Swap-File/portal-gun-4/internet/http/portalguns/assets/1.png

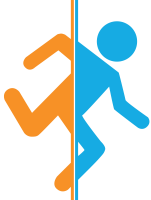
internet/http/portalguns/assets/1.png
