Swap-File/portal-gun-4/internet/http/portalguns/assets/2.png

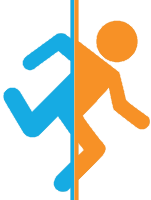
internet/http/portalguns/assets/2.png
