Swap-File/portal-gun-4/internet/http/portalguns/assets/blue_portal.png

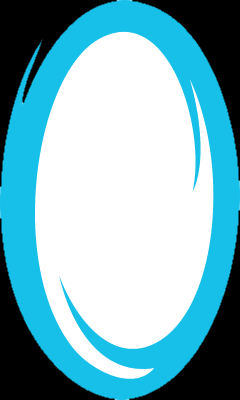
internet/http/portalguns/assets/blue_portal.png
