Swap-File/portal-gun-4/internet/http/portalguns/assets/orange_0.jpg

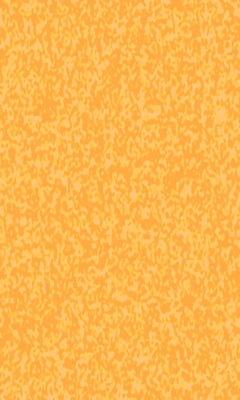
internet/http/portalguns/assets/orange_0.jpg
