Swap-File/portal-gun-4/internet/http/portalguns/assetsp/0.gif

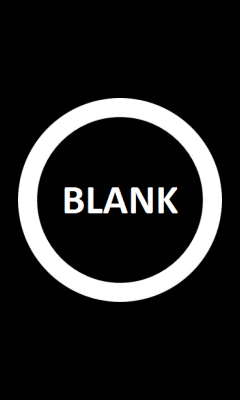
internet/http/portalguns/assetsp/0.gif
