Swap-File/portal-gun-4/internet/http/portalguns/assetsp/1.gif

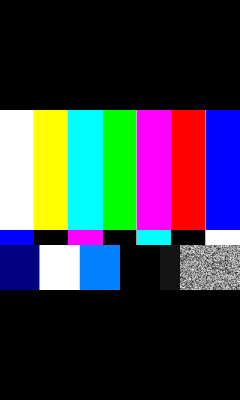
internet/http/portalguns/assetsp/1.gif
