Swap-File/portal-gun-4/internet/http/portalguns/assetsp/2.gif

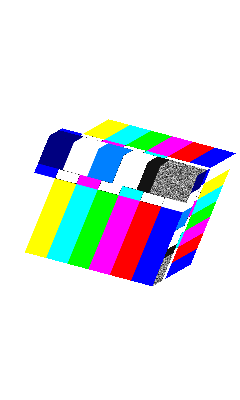
internet/http/portalguns/assetsp/2.gif
