Swap-File/portal-gun-4/internet/http/portalguns/assetsp/3.gif

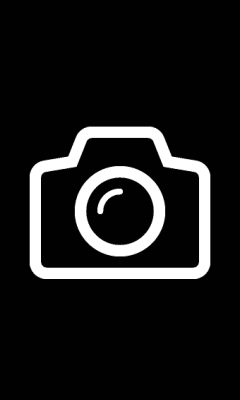
internet/http/portalguns/assetsp/3.gif
