Swap-File/portal-gun-4/internet/http/portalguns/assetsp/4.gif

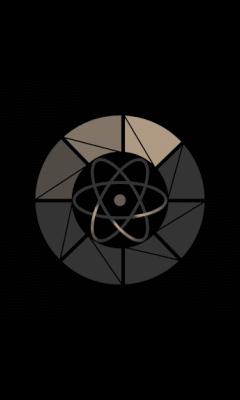
internet/http/portalguns/assetsp/4.gif
