Swap-File/portal-gun-4/internet/http/portalguns/assetsp/7.gif

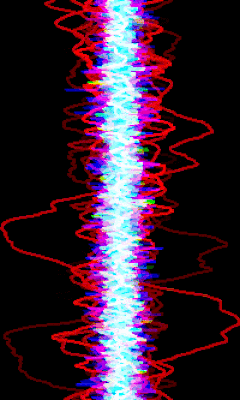
internet/http/portalguns/assetsp/7.gif
