Swap-File/portal-gun-4/internet/http/portalguns/assetsp/8.gif

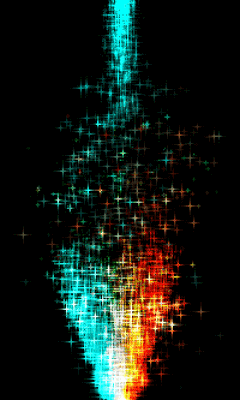
internet/http/portalguns/assetsp/8.gif
