Swap-File/portal-gun-4/internet/http/portalguns/assetsp/9.gif

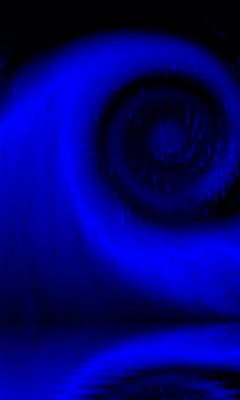
internet/http/portalguns/assetsp/9.gif
