Swap-File/portal-gun-4/internet/http/portalguns/assetsp/10.gif

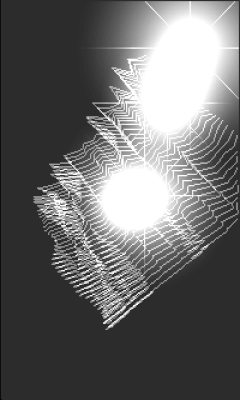
internet/http/portalguns/assetsp/10.gif
