Swap-File/portal-gun-4/internet/http/portalguns/assetsp/11.gif

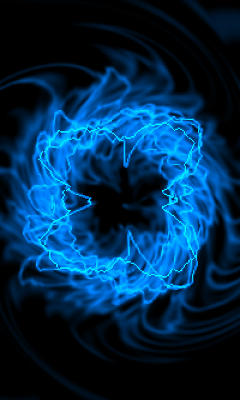
internet/http/portalguns/assetsp/11.gif
