Swap-File/portal-gun-4/internet/http/portalguns/assetsp/12.gif

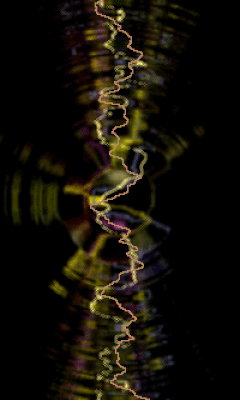
internet/http/portalguns/assetsp/12.gif
