Swap-File/portal-gun-4/internet/http/portalguns/assetsp/13.gif

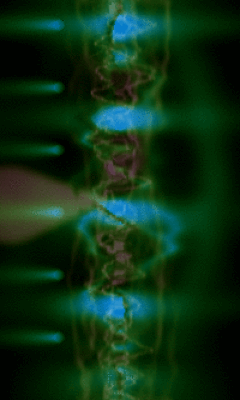
internet/http/portalguns/assetsp/13.gif
