Swap-File/portal-gun-4/internet/http/portalguns/assetsp/14.gif

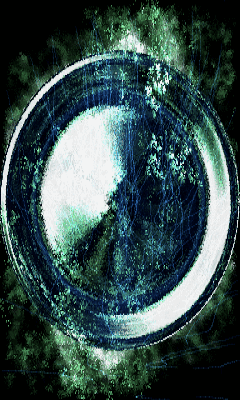
internet/http/portalguns/assetsp/14.gif
