Swap-File/portal-gun-4/internet/http/portalguns/assetsp/15.gif

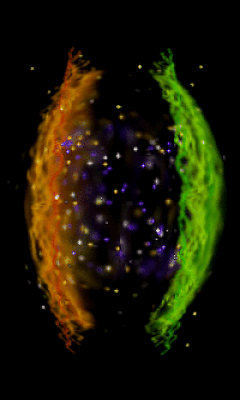
internet/http/portalguns/assetsp/15.gif
