Swap-File/portal-gun-4/internet/http/portalguns/assetsp/17.gif

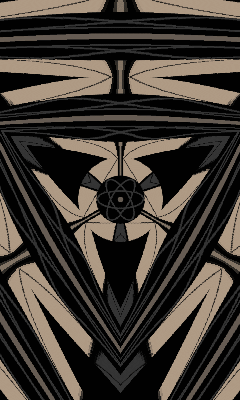
internet/http/portalguns/assetsp/17.gif
