Swap-File/portal-gun-4/internet/http/portalguns/assetsp/19.gif

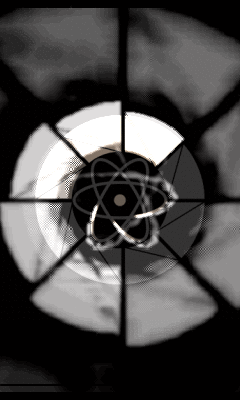
internet/http/portalguns/assetsp/19.gif
