Swap-File/portal-gun-4/internet/http/portalguns/assetsp/20.gif

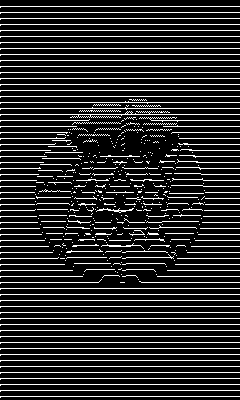
internet/http/portalguns/assetsp/20.gif
