Swap-File/portal-gun-4/internet/http/portalguns/assetsp/21.gif

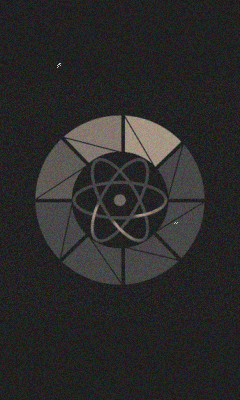
internet/http/portalguns/assetsp/21.gif
