Swap-File/portal-gun-4/internet/http/portalguns/assetsp/22.gif

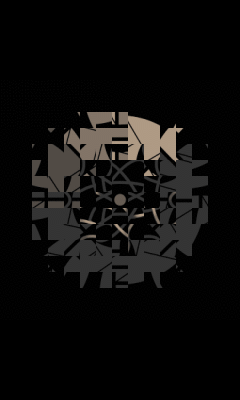
internet/http/portalguns/assetsp/22.gif
