Swap-File/portal-gun-4/internet/http/portalguns/assetsp/24.gif

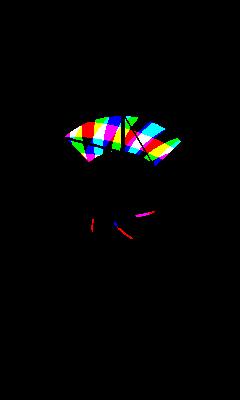
internet/http/portalguns/assetsp/24.gif
