Swap-File/portal-gun-4/internet/http/portalguns/assetsp/25.gif

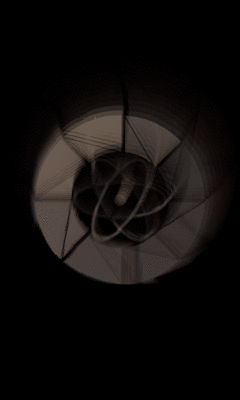
internet/http/portalguns/assetsp/25.gif
