Swap-File/portal-gun-4/internet/http/portalguns/assetsp/28.gif

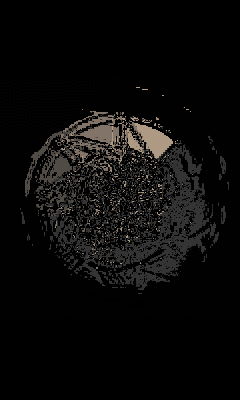
internet/http/portalguns/assetsp/28.gif
