Swap-File/portal-gun-4/internet/http/portalguns/assetsp/29.gif

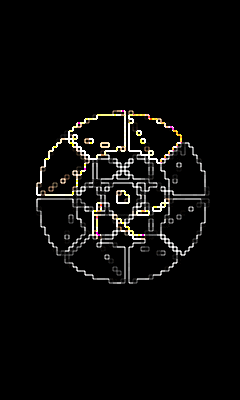
internet/http/portalguns/assetsp/29.gif
