Swap-File/portal-gun-4/internet/http/portalguns/assetsp/30.gif

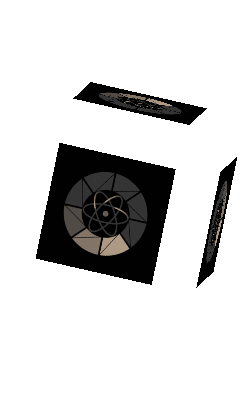
internet/http/portalguns/assetsp/30.gif
