Swap-File/portal-gun-4/internet/http/portalguns/assetsp/31.gif

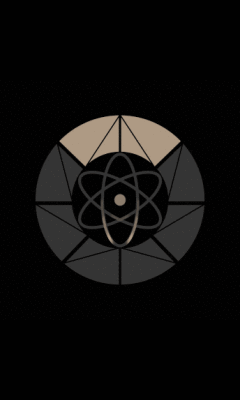
internet/http/portalguns/assetsp/31.gif
