Swap-File/portal-gun-4/internet/http/portalguns/assetsp/32.gif

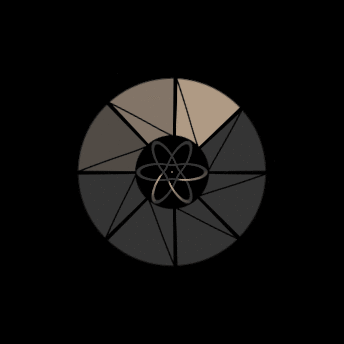
internet/http/portalguns/assetsp/32.gif
