Swap-File/portal-gun-4/internet/http/portalguns/assetsp/33.gif

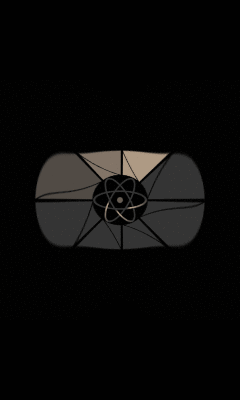
internet/http/portalguns/assetsp/33.gif
