Swap-File/portal-gun-4/internet/http/portalguns/assetsp/34.gif

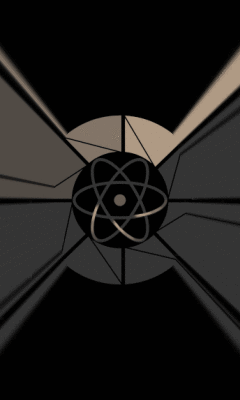
internet/http/portalguns/assetsp/34.gif
