Swap-File/portal-gun-4/internet/http/portalguns/assetsp/36.gif

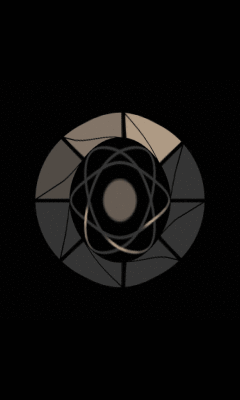
internet/http/portalguns/assetsp/36.gif
