Swap-File/portal-gun-4/internet/http/portalguns/assetsp/50.gif

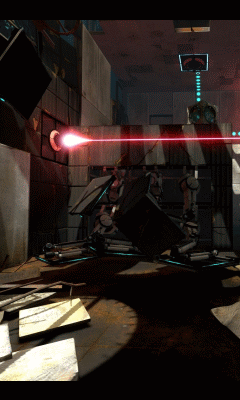
internet/http/portalguns/assetsp/50.gif
