Swap-File/portal-gun-4/internet/http/portalguns/assetsp/51.gif

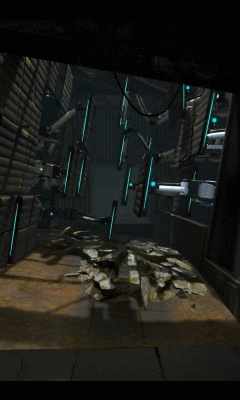
internet/http/portalguns/assetsp/51.gif
