Swap-File/portal-gun-4/internet/http/portalguns/assetsp/52.gif

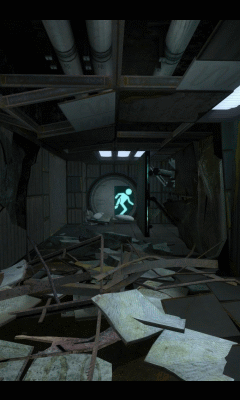
internet/http/portalguns/assetsp/52.gif
