Swap-File/portal-gun-4/internet/http/portalguns/assetsp/54.gif

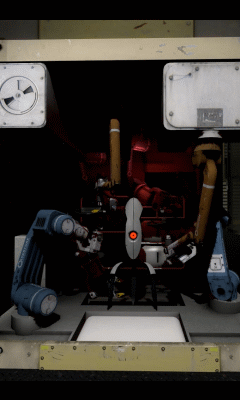
internet/http/portalguns/assetsp/54.gif
