Swap-File/portal-gun-4/internet/http/portalguns/assetsp/55.gif

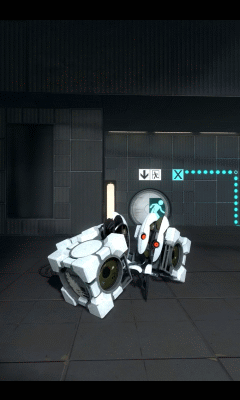
internet/http/portalguns/assetsp/55.gif
