Swap-File/portal-gun-4/internet/http/portalguns/assetsp/56.gif

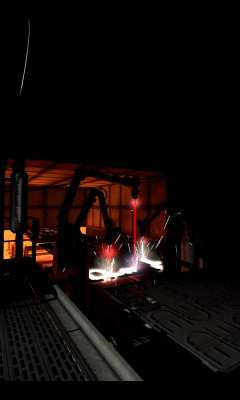
internet/http/portalguns/assetsp/56.gif
