Swap-File/portal-gun-4/internet/http/portalguns/assetsp/57.gif

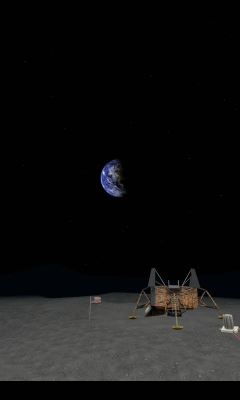
internet/http/portalguns/assetsp/57.gif
