Swap-File/portal-gun-4/internet/http/portalguns/assetsp/58.gif

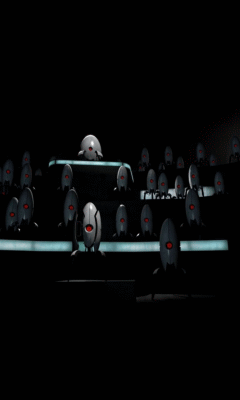
internet/http/portalguns/assetsp/58.gif
