Swap-File/portal-gun-4/internet/http/portalguns/assetsp/59.gif

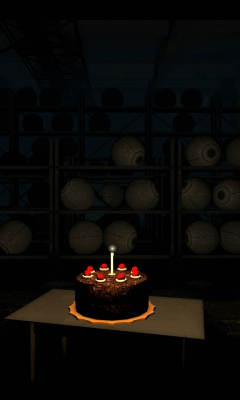
internet/http/portalguns/assetsp/59.gif
