Swap-File/portal-gun-4/internet/http/portalguns/assetsp/60.gif

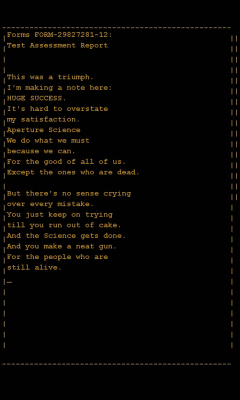
internet/http/portalguns/assetsp/60.gif
