Swap-File/portal-gun-4/internet/http/portalguns/assetsp/61.gif

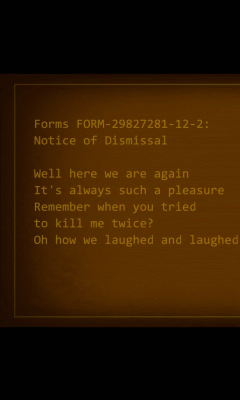
internet/http/portalguns/assetsp/61.gif
