Swap-File/portal-gun-4/internet/http/portalguns/assetsp/-.gif

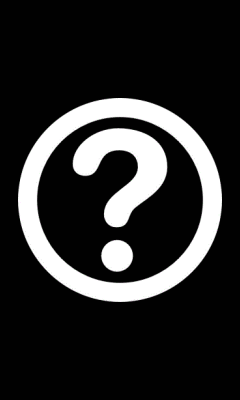
internet/http/portalguns/assetsp/-.gif
