Swap-File/portal-gun-4/internet/http/portalguns/mask.png

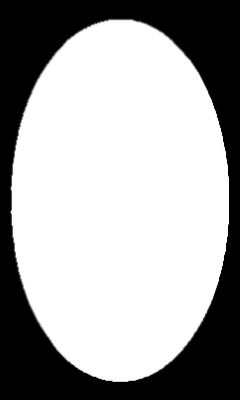
internet/http/portalguns/mask.png
