Swap-File/portal-gun-4/internet/http/portalguns/state1.png

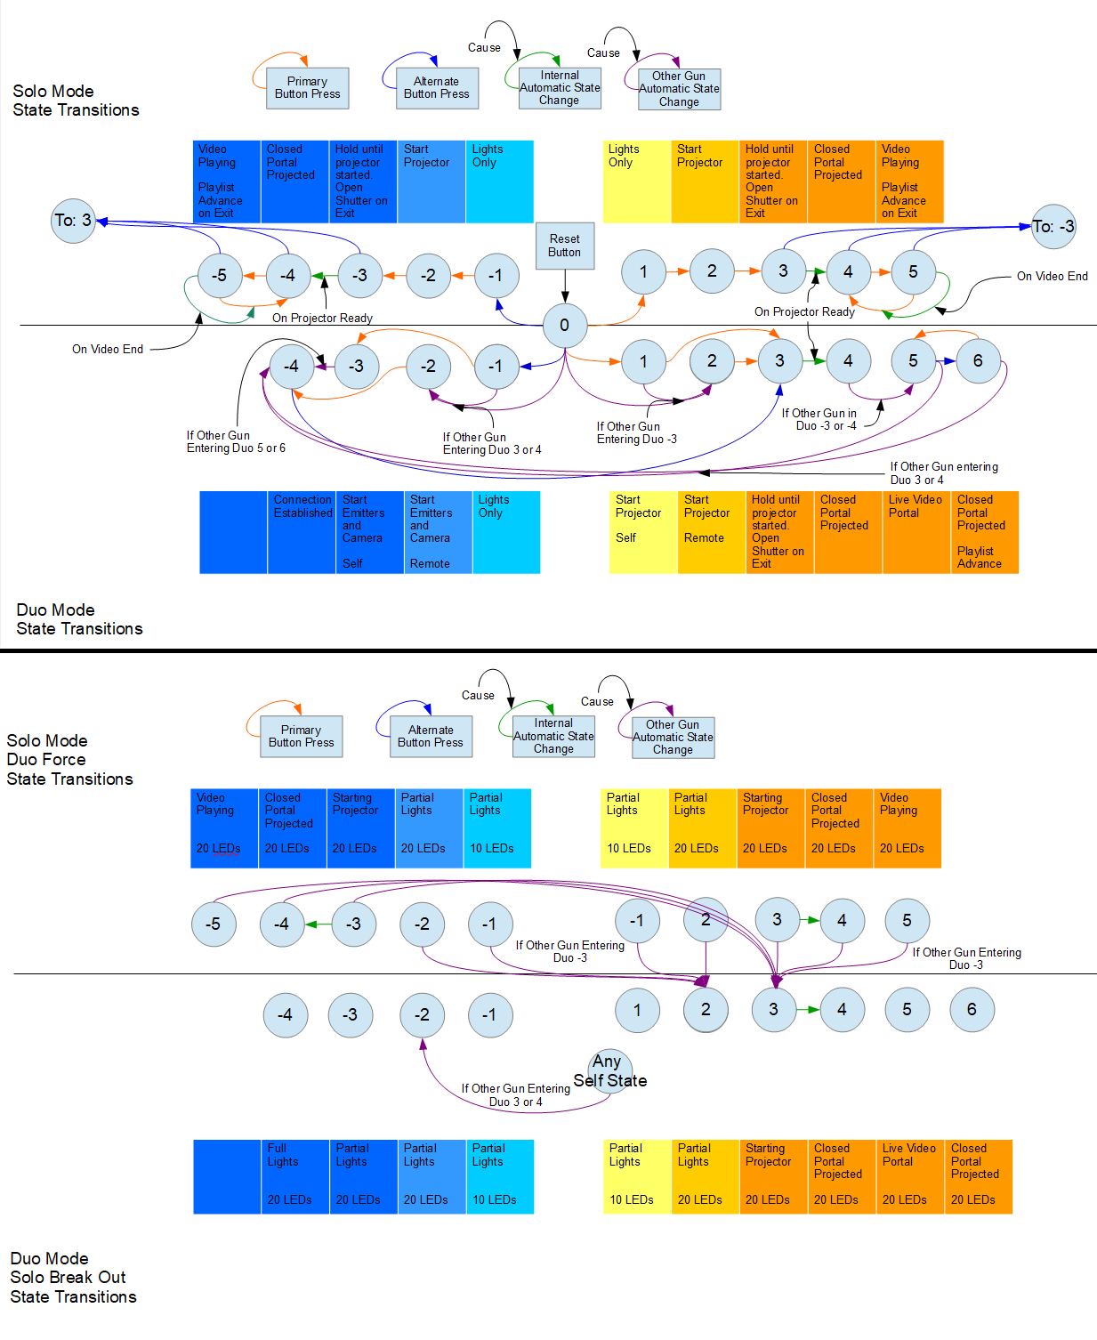
internet/http/portalguns/state1.png
