Swap-File/portal-gun-4/cad/back.SLDPRT

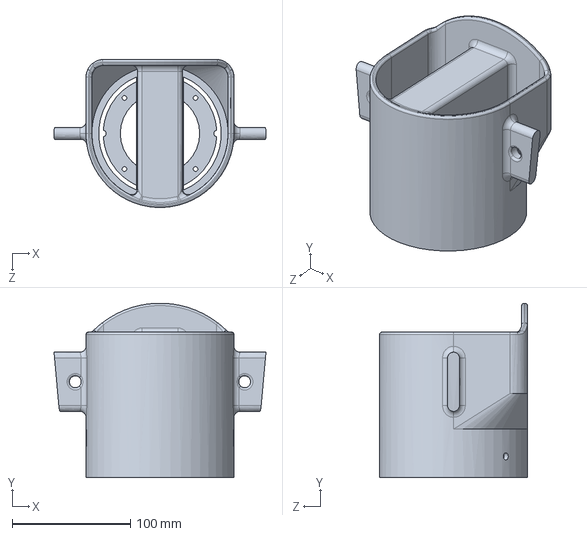
[picture p66: CAD file, 2021-10-30]
cad/back.SLDPRT
179.0 x 147.3 x 125.0 mm
