Swap-File/portal-gun-4/cad/led ring front.SLDPRT

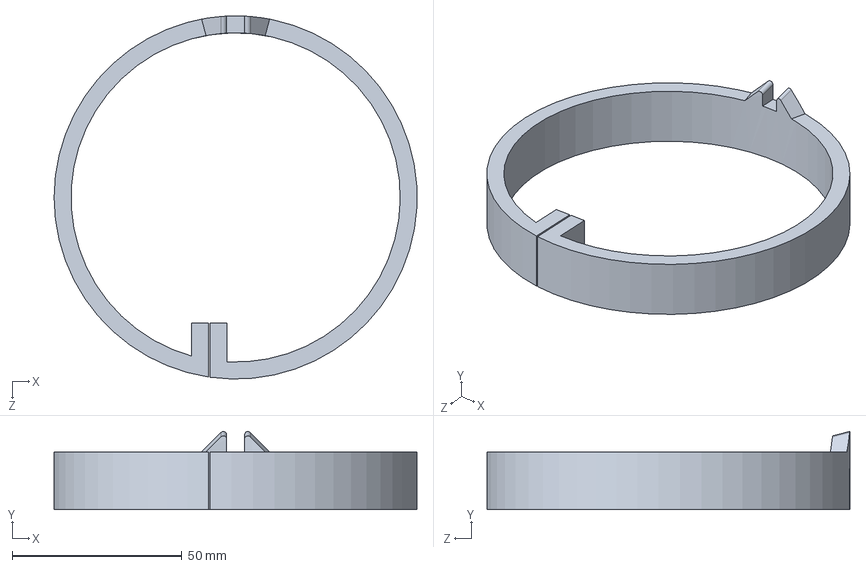
[picture p67: CAD file, 2021-10-30]
cad/led ring front.SLDPRT
106.9 x 23.0 x 107.0 mm
