Swap-File/portal-gun-4/cad/finger gaurd.SLDPRT

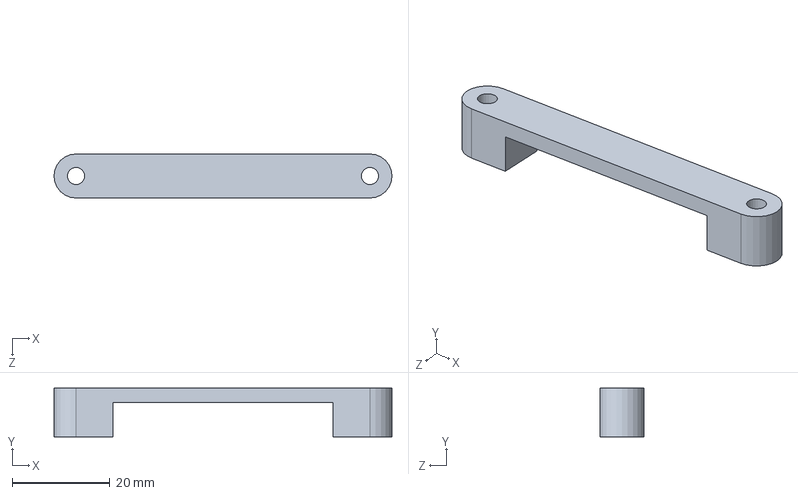
[picture p68: CAD file, 2021-10-30]
cad/finger gaurd.SLDPRT
69.0 x 10.0 x 9.00 mm
