Swap-File/portal-gun-4/cad/stand.SLDPRT

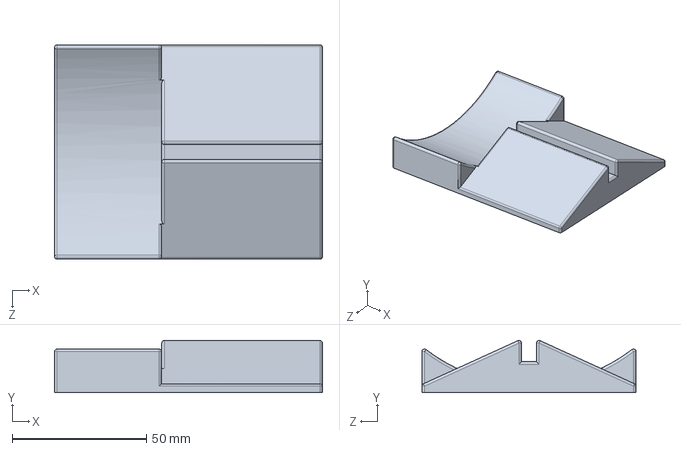
[picture p69: CAD file, 2021-10-30]
cad/stand.SLDPRT
100.0 x 19.4 x 80.0 mm
