Swap-File/portal-gun-4/cad/tool.SLDPRT

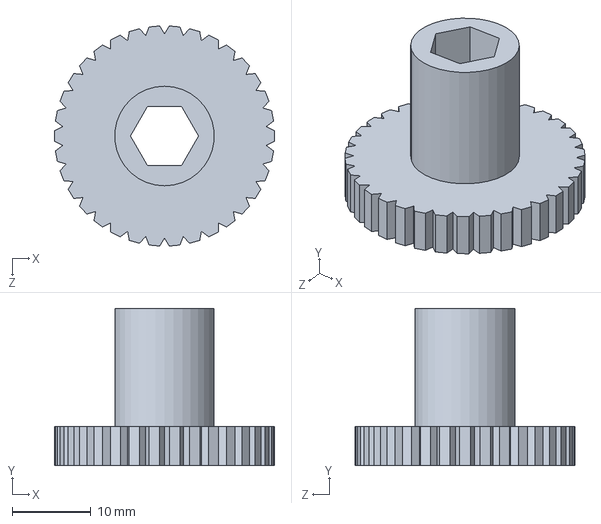
[picture p70: CAD file, 2021-10-30]
cad/tool.SLDPRT
28.0 x 20.0 x 28.0 mm
