Swap-File/portal-gun-4/portal/common/common.h

/*
 * Copyright (c) 2017 Rob Clark <rclark@redhat.com>
 *
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
 * THE SOFTWARE IS PROVIDED "AS IS", WITHOUT WARRANTY OF ANY KIND, EXPRESS OR
 * IMPLIED, INCLUDING BUT NOT LIMITED TO THE WARRANTIES OF MERCHANTABILITY,
 * FITNESS FOR A PARTICULAR PURPOSE AND NON-INFRINGEMENT. IN NO EVENT SHALL
 * THE AUTHORS OR COPYRIGHT HOLDERS BE LIABLE FOR ANY CLAIM, DAMAGES OR OTHER
 * LIABILITY, WHETHER IN AN ACTION OF CONTRACT, TORT OR OTHERWISE, ARISING
 * FROM, OUT OF OR IN CONNECTION WITH THE SOFTWARE OR THE USE OR OTHER
 * DEALINGS IN THE SOFTWARE.
 */

#ifndef _COMMON_H
#define _COMMON_H
#include "../common/drm-common.h"
#include <drm_fourcc.h>
#include <GLES3/gl31.h>
#include <GLES2/gl2ext.h>
#include <EGL/egl.h>
#include <EGL/eglext.h>

#include <gbm.h>
//#include <drm_fourcc.h>
#include <stdbool.h>

#define ARRAY_SIZE(arr) (sizeof(arr) / sizeof((arr)[0]))

/* from mesa's util/macros.h: */
#define MIN2( A, B )   ( (A)<(B) ? (A) : (B) )
#define MAX2( A, B )   ( (A)>(B) ? (A) : (B) )
#define MIN3( A, B, C ) ((A) < (B) ? MIN2(A, C) : MIN2(B, C))
#define MAX3( A, B, C ) ((A) > (B) ? MAX2(A, C) : MAX2(B, C))

static inline unsigned
u_minify(unsigned value, unsigned levels)
{
	return MAX2(1, value >> levels);
}

#ifndef EGL_KHR_platform_gbm
#define EGL_KHR_platform_gbm 1
#define EGL_PLATFORM_GBM_KHR              0x31D7
#endif /* EGL_KHR_platform_gbm */

#ifndef EGL_EXT_platform_base
#define EGL_EXT_platform_base 1
typedef EGLDisplay (EGLAPIENTRYP PFNEGLGETPLATFORMDISPLAYEXTPROC) (EGLenum platform, void *native_display, const EGLint *attrib_list);
typedef EGLSurface (EGLAPIENTRYP PFNEGLCREATEPLATFORMWINDOWSURFACEEXTPROC) (EGLDisplay dpy, EGLConfig config, void *native_window, const EGLint *attrib_list);
typedef EGLSurface (EGLAPIENTRYP PFNEGLCREATEPLATFORMPIXMAPSURFACEEXTPROC) (EGLDisplay dpy, EGLConfig config, void *native_pixmap, const EGLint *attrib_list);
#ifdef EGL_EGLEXT_PROTOTYPES
EGLAPI EGLDisplay EGLAPIENTRY eglGetPlatformDisplayEXT (EGLenum platform, void *native_display, const EGLint *attrib_list);
EGLAPI EGLSurface EGLAPIENTRY eglCreatePlatformWindowSurfaceEXT (EGLDisplay dpy, EGLConfig config, void *native_window, const EGLint *attrib_list);
EGLAPI EGLSurface EGLAPIENTRY eglCreatePlatformPixmapSurfaceEXT (EGLDisplay dpy, EGLConfig config, void *native_pixmap, const EGLint *attrib_list);
#endif
#endif /* EGL_EXT_platform_base */

#ifndef EGL_VERSION_1_5
#define EGLImage EGLImageKHR
#endif /* EGL_VERSION_1_5 */

#define WEAK __attribute__((weak))

/* Define tokens from EGL_EXT_image_dma_buf_import_modifiers */
#ifndef EGL_EXT_image_dma_buf_import_modifiers
#define EGL_EXT_image_dma_buf_import_modifiers 1
#define EGL_DMA_BUF_PLANE3_FD_EXT         0x3440
#define EGL_DMA_BUF_PLANE3_OFFSET_EXT     0x3441
#define EGL_DMA_BUF_PLANE3_PITCH_EXT      0x3442
#define EGL_DMA_BUF_PLANE0_MODIFIER_LO_EXT 0x3443
#define EGL_DMA_BUF_PLANE0_MODIFIER_HI_EXT 0x3444
#define EGL_DMA_BUF_PLANE1_MODIFIER_LO_EXT 0x3445
#define EGL_DMA_BUF_PLANE1_MODIFIER_HI_EXT 0x3446
#define EGL_DMA_BUF_PLANE2_MODIFIER_LO_EXT 0x3447
#define EGL_DMA_BUF_PLANE2_MODIFIER_HI_EXT 0x3448
#define EGL_DMA_BUF_PLANE3_MODIFIER_LO_EXT 0x3449
#define EGL_DMA_BUF_PLANE3_MODIFIER_HI_EXT 0x344A
#endif

struct gbm {
	struct gbm_device *dev;
	struct gbm_surface *surface;
	uint32_t format;
	int width, height;
};

const struct gbm * init_gbm(int drm_fd, int w, int h, uint32_t format, uint64_t modifier);


struct egl {
	EGLDisplay display;
	EGLConfig config;
	EGLContext context;
	EGLSurface surface;

	
	PFNEGLGETPLATFORMDISPLAYEXTPROC eglGetPlatformDisplayEXT;
	PFNEGLCREATEIMAGEKHRPROC eglCreateImageKHR;
	PFNEGLDESTROYIMAGEKHRPROC eglDestroyImageKHR;
	PFNGLEGLIMAGETARGETTEXTURE2DOESPROC glEGLImageTargetTexture2DOES;
	PFNEGLCREATESYNCKHRPROC eglCreateSyncKHR;
	PFNEGLDESTROYSYNCKHRPROC eglDestroySyncKHR;
	PFNEGLWAITSYNCKHRPROC eglWaitSyncKHR;
	PFNEGLCLIENTWAITSYNCKHRPROC eglClientWaitSyncKHR;
	PFNEGLDUPNATIVEFENCEFDANDROIDPROC eglDupNativeFenceFDANDROID;

	bool modifiers_supported;

	void (*draw)(unsigned i,char *debug_stdin);
};

static inline int __egl_check(void *ptr, const char *name)
{
	if (!ptr) {
		printf("no %s\n", name);
		return -1;
	}
	return 0;
}

#define egl_check(egl, name) __egl_check((egl)->name, #name)

int init_egl(struct egl *egl, const struct gbm *gbm, int samples);
int create_program(const char *vs_src, const char *fs_src);
int link_program(unsigned program);

enum mode {
	SMOOTH,        /* smooth-shaded */
	RGBA,          /* single-plane RGBA */
	NV12_2IMG,     /* NV12, handled as two textures and converted to RGB in shader */
	NV12_1IMG,     /* NV12, imported as planar YUV eglimg */
	VIDEO,         /* video textured cube */
};

#endif /* _COMMON_H */
