Swap-File/portal-gun-4/portal/common/gstcontext.h

#ifndef _GSTCONTEXT_H
#define _GSTCONTEXT_H

#include <stdbool.h>
#include <gst/gst.h> //GstPipeline
#include <EGL/egl.h>   //EGLDisplay & EGLContext
#include <GLES3/gl31.h> //GLint

void gstcontext_set(GstPipeline **pipeline);
void gstcontext_load_pipeline(int index, GstPipeline **pipeline, GstState state,char * text);
void gstcontext_init(EGLDisplay display, EGLContext context,volatile GLint *temp_texture_id,volatile bool *temp_texture_fresh,volatile bool *temp_video_done_flag);
void gstcontext_handle_bus(GstPipeline **pipeline);

#endif
